lshw/18650/docs/18650.jpg

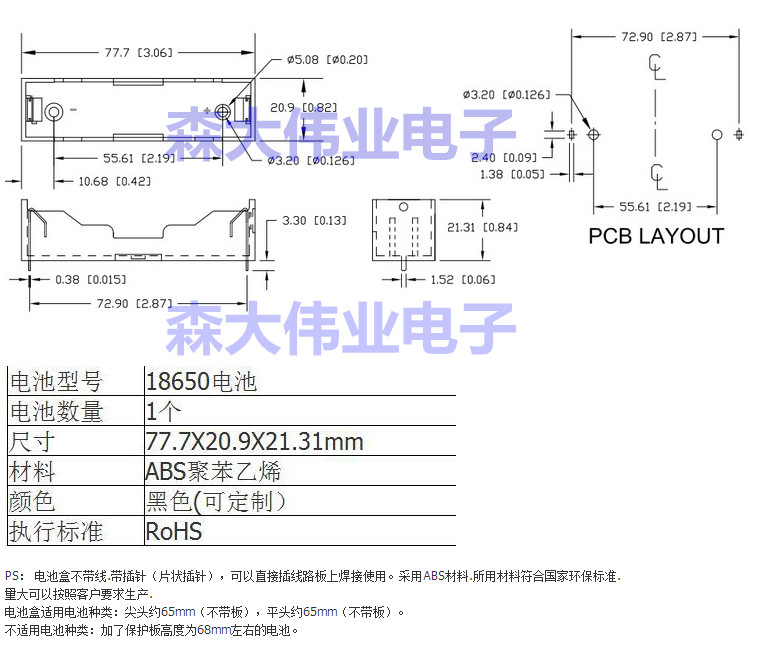
docs/18650.jpg
