lshw/18650/pcb/5usb2.png

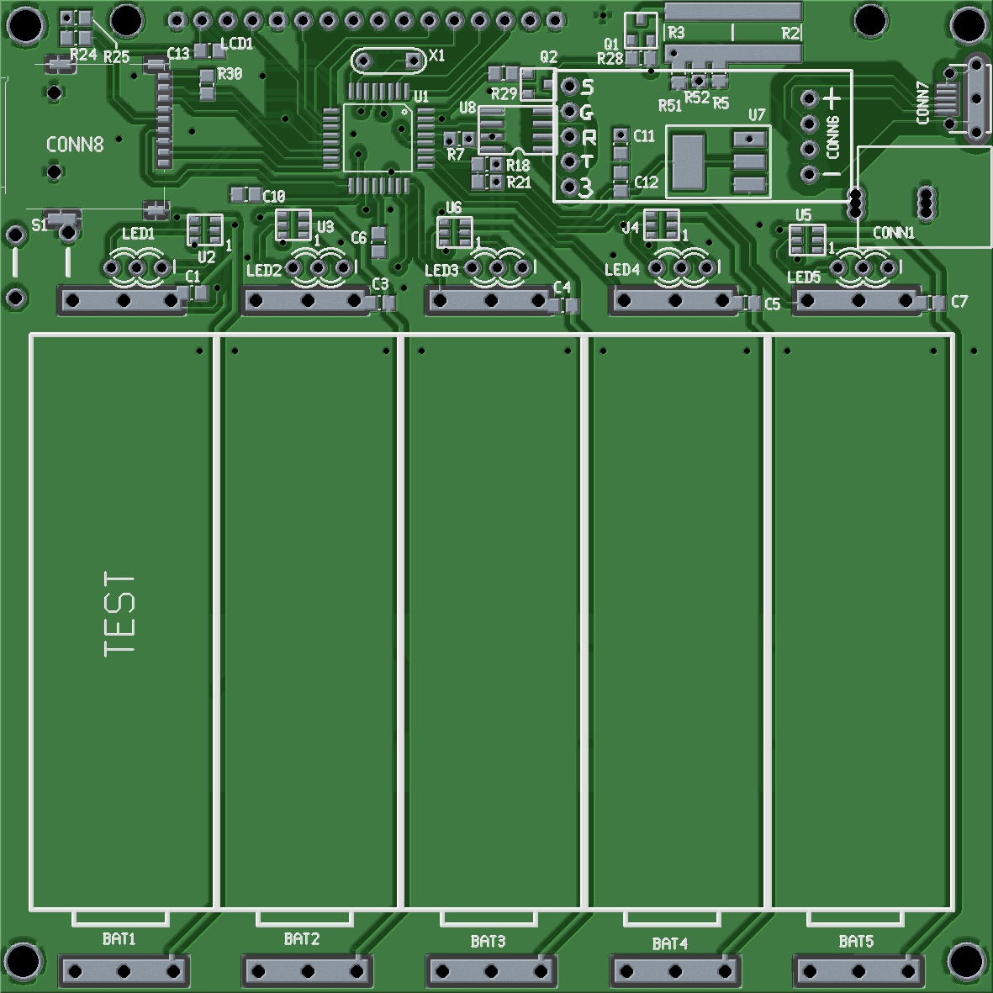
pcb/5usb2.png
