lshw/18650/pcb/5usb2a.png

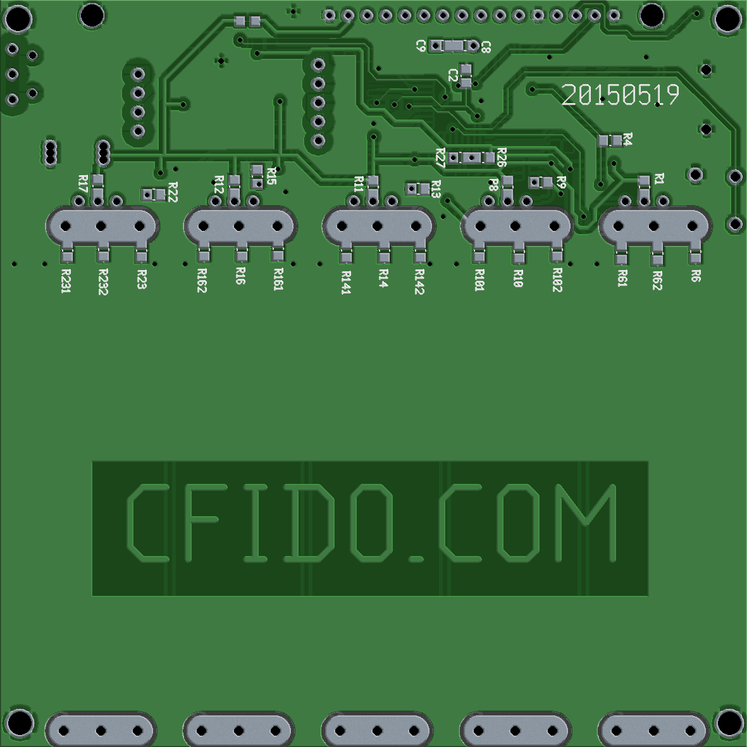
pcb/5usb2a.png
