lshw/18650/pcb/5usb.png

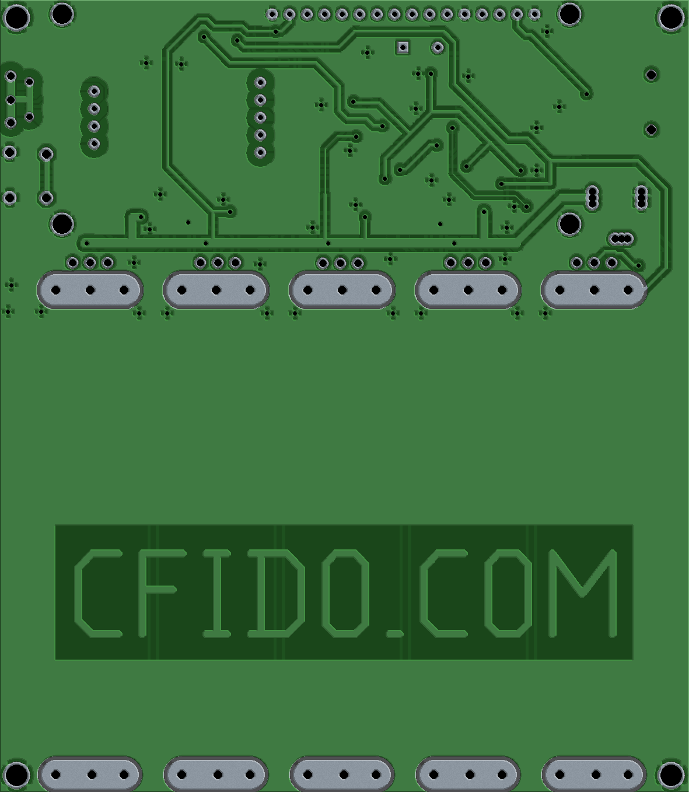
pcb/5usb.png
