lshw/18650/pcb/5usb_sch.png

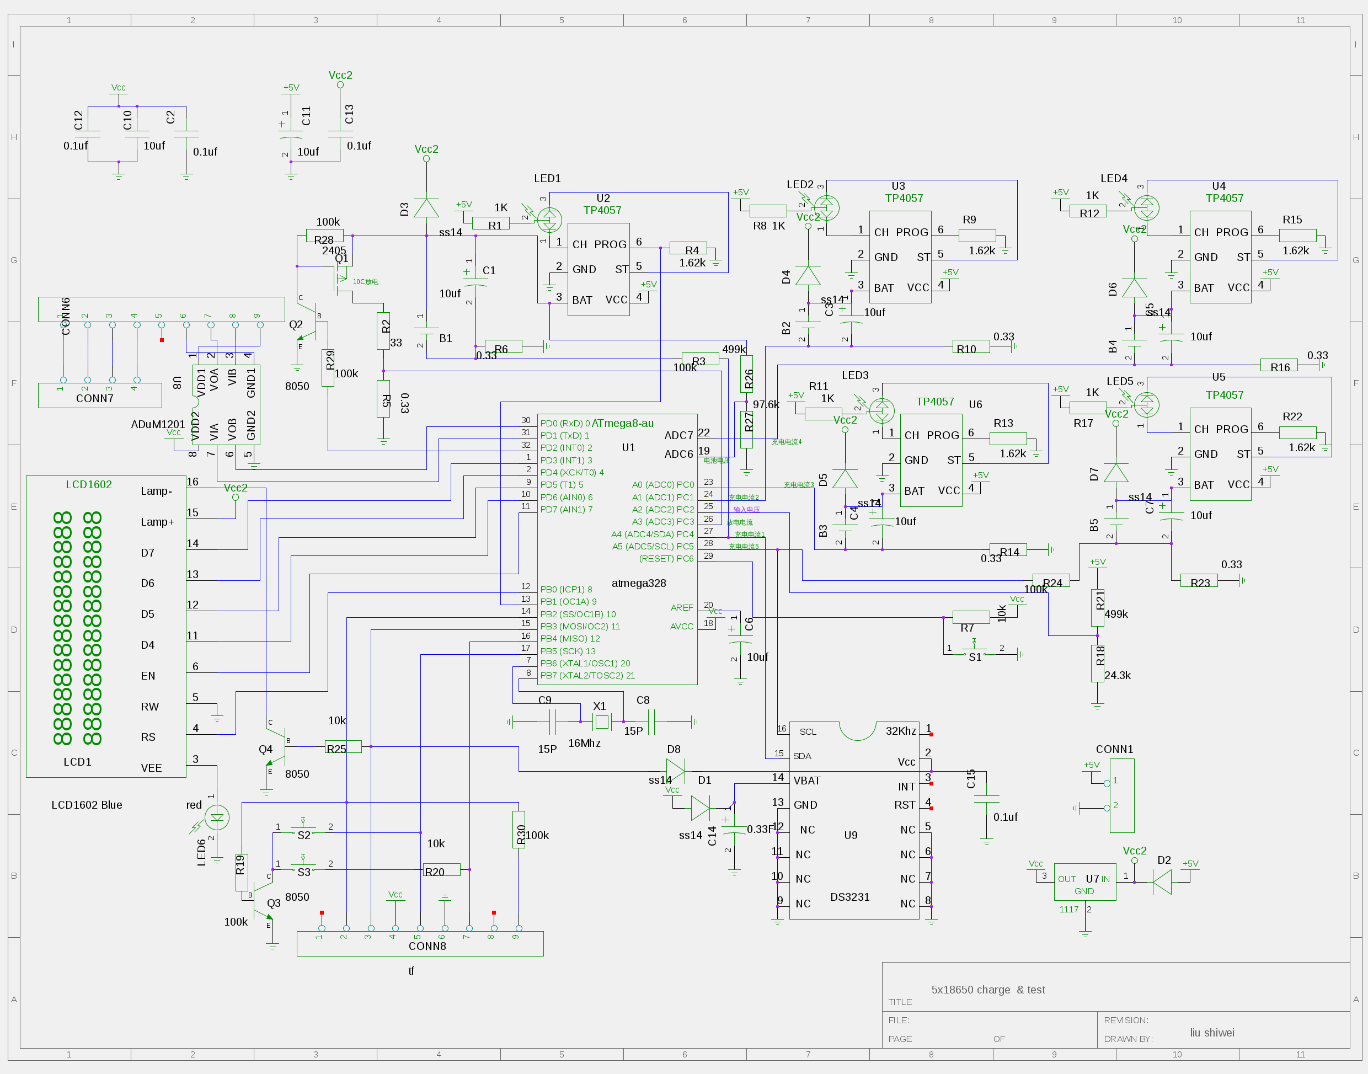
pcb/5usb_sch.png
