lshw/18650/scad/lcd_foot.scad

$fn=40;
difference() {
cylinder(h=11,r=3);
cylinder(h=11,r=1.5);
}
difference() {
cylinder(h=2,r=3.5);
cylinder(h=3,r=1.5);
}
